daid/SpiderCart/sw/firmware/src/coprocessor.cpp

#include "coprocessor.h"
#include "romload.h"
#include "mbc.h"
#include "mbc_prepare.h"
#include "command.h"
#include "p8.h"
#include "accelerometer.h"

#include "usb_msc.h"
#include "filesystem.h"
#include <stdlib.h>
#include <pico/multicore.h>
#include <string.h>
#include <stdio.h>
#include <ctype.h>
#include <stdarg.h>


uint8_t ram_data[16 * 0x2000];

enum class SavState {
    Idle,
    WaitTillSave,
    PostSaveDelay,
} sav_state = SavState::Idle;
absolute_time_t sav_timer;

bool valid_rom_ext(const char* ext)
{
    if (strcasecmp(ext, ".gb") == 0) return true;
    if (strcasecmp(ext, ".gbc") == 0) return true;
    if (strcasecmp(ext, ".png") == 0) {
        if (tolower(ext[-1]) == '8' && tolower(ext[-2]) == 'p' && tolower(ext[-3]) == '.') {
            return true;
        }
    }
    return false;
}

int co_error(int error_nr, const char* fmt, ...)
{
    va_list arg_ptr;

    va_start(arg_ptr, fmt);
    vsnprintf((char*)&ram_data[15 * 0x2000 + 0x1F00], 0xF0, fmt, arg_ptr);
    printf("%s\n", (char*)&ram_data[15 * 0x2000 + 0x1F00]);
    va_end(arg_ptr);

    ram_data[15 * 0x2000 + 0x1FFF] = error_nr; // indicate an error
    return error_nr;
}

static uint16_t mbc7_ram[128];
void processMBC7_eeprom(volatile uint8_t* mem)
{
    disable_interrupts();
    int bit_mask = 1;
    int bits = 0;
    int read_bits = 1;
    while(true) {
        auto value = *mem;
        if (!(value & 0x80)) break; //CS gone

        if ((value & 0x40) == 0x40) { //CLK low->high
            //Clock in a bit
            if (value & 2) bits |= bit_mask;
            if (bits) bit_mask <<= 1;

            if (bit_mask == 0x00000800) {
                read_bits = mbc7_ram[(bits >> 4) & 0x7F] << 12;
            }
            if (bit_mask == 0x08000000) {
                if ((bits & 0x07) == 0x05) {
                    mbc7_ram[(bits >> 4) & 0x7F] = bits >> 11;
                }
            }
            if (read_bits & bit_mask) {
//                *mem |= 0x01;
            }
            // while((*mem) & 0x40) {} //Wait till CLK high->low 
            if (read_bits & bit_mask) {
//                *mem |= 0x01;
            }
        }
    }
    *mem |= 0x01;
    enable_interrupts();
}

void processCoProcessor()
{
    switch(sav_state) {
    case SavState::Idle: break;
    case SavState::WaitTillSave:
        if (absolute_time_diff_us(get_absolute_time(), sav_timer) < 0) {
            printf("Saving sram");
            save_sav(mbc_ram_bank_mask + 1);
            sav_state = SavState::PostSaveDelay;
            sav_timer = make_timeout_time_ms(10000);
        }
        break;
    case SavState::PostSaveDelay:
        if (absolute_time_diff_us(get_absolute_time(), sav_timer) < 0) {
            sav_state = SavState::Idle;
        }
        break;
    }

    if (multicore_fifo_rvalid()) {
        auto cmd = sio_hw->fifo_rd;
        if (cmd == 0) {
            // request to save SRAM
            if (sav_state == SavState::Idle) {
                sav_state = SavState::WaitTillSave;
                sav_timer = make_timeout_time_ms(100);
            }
            if (sav_state == SavState::PostSaveDelay) {
                sav_state = SavState::WaitTillSave;
            }
        } else if (cmd == 1) {
            auto ptr = ram_data + 0x2000 * 0x08;
            *ptr++ = 0; //seconds
            *ptr++ = 0; //minutes
            *ptr++ = 0; //hours
            *ptr++ = 0; //day counter
            *ptr++ = 0; //flags/state
            for(int n=0; n<16-5; n++)
                *ptr++ = 0;
        } else if (cmd == 3) { //MBC7 update
            if (ram_data[0x0080] & 0x80) {
                //processMBC7_eeprom((volatile uint8_t*)&ram_data[0x0080]);
            }
            //ram_data[0x0080] |= 0x01;
            if (ram_data[0x0000] == 0x55) {
                ram_data[0x0000] = 0;
                ram_data[0x0020] = 0x00;
                ram_data[0x0030] = 0x80;
                ram_data[0x0040] = 0x00;
                ram_data[0x0050] = 0x80;
                ram_data[0x0060] = 0x00;
                ram_data[0x0070] = 0xFF;
            }
            if (ram_data[0x0010] == 0xAA) {
                ram_data[0x0010] = 0;
                //Accelerometer update, enable and read out the LIS3DH
                int16_t data[3];
                accelerometer_read(data);
                printf("%04x %04x %04x\n", data[0], data[1], data[2]);
                data[0] = 0x0700 - (data[0] >> 7);
                data[1] = 0x0700 - (data[1] >> 7);
                ram_data[0x0020] = data[0];
                ram_data[0x0030] = data[0] >> 8;
                ram_data[0x0040] = data[1];
                ram_data[0x0050] = data[1] >> 8;
            }
        } else if (cmd & 0x100) {
            switch(cmd & 0xFF) {
            case COMMAND_LIST_DIR:
                {
                    auto* ptr = ram_data;
                    size_t data_index = 0x2000;
                    ReadDir dir("/");
                    for(auto entry = dir.read(); entry.name[0]; entry = dir.read()) {
                        if (entry.directory) {
                            *ptr++ = 0x02;
                            *ptr++ = data_index >> 13;
                            *ptr++ = data_index & 0xFF;
                            *ptr++ = ((data_index >> 8) & 0x1F) | 0xA0;
                            strcpy((char*)ram_data + data_index, entry.name);
                            data_index += strlen(entry.name) + 1;
                        } else {
                            auto ext = strrchr(entry.name, '.');
                            if (ext && valid_rom_ext(ext)) {
                                *ptr++ = 0x01;
                                *ptr++ = data_index >> 13;
                                *ptr++ = data_index & 0xFF;
                                *ptr++ = ((data_index >> 8) & 0x1F) | 0xA0;
                                strcpy((char*)ram_data + data_index, entry.name);
                                data_index += strlen(entry.name) + 1;
                            }
                        }
                    }
                    *ptr = 0;
                    qsort(ram_data, (ptr - ram_data) / 32, 32, [](const void* a, const void* b) -> int {
                        auto aa = (const char*)a;
                        auto bb = (const char*)b;
                        if (*aa != *bb) return *aa - *bb;
                        return strcmp(aa+1, bb+1);
                    });
                    ram_data[15 * 0x2000 + 0x1FFF] = 0;
                }
                break;
            case COMMAND_LOAD_AND_RESET:
                stop_mbc();
                if (load_rom((const char*)&ram_data[15 * 0x2000])) {
                    start_mbc(false);
                } else {
                    ram_data[15 * 0x2000 + 0x1FFF] = 0;
                    prepare_mbc();
                    if (mbc_flags & MBC_FLAG_BATTERY) {
                        load_sav();
                    }
                    start_mbc(true);
                }
                break;
            case COMMAND_LOAD_FOR_QUICKBOOT:
                stop_mbc();
                ram_data[15 * 0x2000 + 0x1FFF] = 0;
                load_rom((const char*)&ram_data[15 * 0x2000]);
                start_mbc(false);
                break;
            case COMMAND_EXEC_QUICKBOOT:
                stop_mbc();
                prepare_mbc();
                ram_data[15 * 0x2000 + 0x1FFF] = 0;
                if (mbc_flags & MBC_FLAG_BATTERY) {
                    load_sav();
                }
                start_mbc(false);
                break;
            case COMMAND_SET_USB_MSC:
                set_usb_msc_enable(ram_data[15 * 0x2000] != 0);
                ram_data[15 * 0x2000 + 0x1FFF] = 0;
                break;
            case COMMAND_P8_CYCLE_60:
                p8_cycle60();
                break;
            case COMMAND_P8_CYCLE_30:
                p8_cycle30();
                break;
            case COMMAND_P8_RENDER:
                p8_render();
                break;
            default:
                co_error(1, "Unknown command: %x", cmd);
                break;
            }
        }
    }
}
