daid/SpiderCart/sw/firmware/inc/command.h

#pragma once

#define COMMAND_LIST_DIR           0x01
#define COMMAND_LOAD_AND_RESET     0x10
#define COMMAND_LOAD_FOR_QUICKBOOT 0x11
#define COMMAND_SET_USB_MSC        0x20
#define COMMAND_EXEC_QUICKBOOT     0xF0
#define COMMAND_P8_CYCLE_60        0x80
#define COMMAND_P8_CYCLE_30        0x81
#define COMMAND_P8_RENDER          0x82
